CyberWei922/ESP32S3_KVM_desktop_controller/esp32/latest/docs/development_plan.md

# v0.5.0-dev.22 开发计划

## 阶段A：规格冻结

- [x] 视觉年代固定为System 7，并辅以少量System 1元素。
- [x] 屏幕语言固定为纯英文。
- [x] UI结构冻结为SYSTEM、WEATHER、MARKETS三页仪表盘。
- [x] 固定LVGL 9.3.0和ESP-IDF组件集成方式；字体与图标资源已纳入源码。
- [x] 冻结散热器四模式、按键判定、上电归一化和自动控温设计，见`cooler_control_spec.md`。
- [ ] 实测散热器双击、关机长按、组间隔和上电等待时序。
- [x] 关闭状态要求物理熄灭背光，不接受仅绘制黑色画面。
- [x] ILI9341V软件背光命令实机无效，排除纯SPI控制方案。
- [x] BLK接地电流实测约0.2mA，GPIO15开漏直接控制已完成实机开/关验证。
- [ ] 完成GPIO15重复开关与长时间运行验收。

## 阶段B：显示系统

- [x] 创建ESP-IDF v6.1工程。
- [x] 接入LVGL和ILI9341 flush回调。
- [x] 完成SYSTEM、WEATHER、MARKETS三页复古界面并验证编译。
- [ ] 刷写实机后检查内存、帧率和连续运行。

## 阶段C：服务移植

- [x] 按模块移植状态、Wi-Fi、WebSocket、protocol v1和按钮驱动。
- [x] 建立语义事件队列和单一LVGL任务。
- [x] 加入两路继电器安全驱动与截止保护。
- [x] 加入dashboard序号校验、Windows主源和Mac备用源切换。
- [x] 加入display_sleep/display_wake能力协商和结果汇总。

## 阶段D：页面与交互

- [x] 完成SYSTEM、WEATHER、MARKETS三页仪表盘。
- [x] 启用中键单击下一页、双击上一页。
- [x] 完成左键KVM状态机。
- [x] 按`cooler_control_spec.md`实现GPIO8状态机；继电器延时不放入UI任务。
- [x] 加入错误、离线、未知、校准和冷却反馈。
- [ ] 完成刷写后的整机交互验收。

## 阶段E：首版整机验收

- 联调Mac、Windows、DDC和USB；确认散热器UI不触发GPIO8。
- 完成100次KVM切换与24小时运行。
- 验收后冻结版本，更新根目录路线和版本记录。

## 当前扩展：双主机显示待机与唤醒

- [x] 实测确认：X41Q在仍有Windows DP信号时会从Mac自动跳到DP；所有输入均停止后进入闪灯待机。
- [x] 冻结“双客户端停止视频输出、只唤醒目标主机”的设计，见`display_sleep_plan.md`。
- [x] 以protocol v1可选能力协商扩展`display_sleep`和`display_wake`命令及可诊断结果。
- [x] Mac客户端实现只关闭/恢复显示输出，不让整机睡眠。
- [ ] Windows托盘客户端实现只关闭/恢复显示输出，并在黑屏期间保持在线。
- [x] ESP32实现双客户端并行休眠、结果汇总、目标单机唤醒和错误状态机。
- [x] 将左键长按背光开关与显示待机状态机绑定；黑屏期间锁定所有按键，只保留左键长按唤醒。
- [x] 唤醒时默认只恢复关屏前当前主机的视频输出，不同时恢复两路。
- [ ] 完成20次待机及Mac/Windows各10次定向唤醒验收。

## 暂缓项：刷新同步背光补偿

状态：已写入`v0.5.0-dev.22`固件和macOS客户端，等待Windows客户端实现与三端实机验收。

### 已确认事实

- 厂商风格隔离测试固件已实机确认：GPIO15以20kHz PWM输出时，BLK能够呈现三个清晰亮度档位，说明本机实物支持通过BLK进行PWM亮度控制。
- 最精简的软件SPI测试在真实像素刷新瞬间仍会闪烁，因此问题不依赖LVGL、Wi-Fi或DMA；刷新期间的电气负载变化仍是待补偿对象。

### 临时参数（不是最终校准值）

- PWM频率：20kHz。
- 静态/非刷新亮度：60%占空比，暂时固定。
- 刷新期间亮度：初始验证可从100%占空比开始，最终值必须根据实机结果调整。
- 这些参数只能集中定义，禁止散落为魔法数字。

### 计划实现方式

- 在一次有效画面更新开始、首笔像素传输之前切换到“刷新亮度”。
- 在本次画面更新的最后一个刷新区块完成后恢复60%“静态亮度”。
- 不得在同一次LVGL更新的每个分块之间反复恢复60%，避免补偿本身产生闪烁。
- 背光开关状态优先级高于补偿：用户关闭背光后，任何刷新都不得重新点亮。

### 必须完成的刷新面积实测

刷新面积可能改变瞬时负载、传输持续时间和肉眼感受到的亮度下降，因此不能假设所有区块共用同一个补偿值。实施时至少分别记录：

1. 极小刷新：单个状态图标、短文本或中央小方块。
2. 中等刷新：一行Live Data、进度条或一个信息框。
3. 多分块刷新：同一UI状态变更触发多个区域连续传输。
4. 全屏刷新：开机页切换或完整界面重绘。

每组记录刷新像素数、总传输时长、静态占空比、刷新占空比以及肉眼结果（偏暗、持平或偏亮）。如果不同面积所需补偿明显不同，再决定采用：

- 单一固定刷新占空比；或
- 按刷新像素数/传输时长分为小、中、全屏三档补偿。

### 验收条件

- 小区域、中区域、多分块和全屏刷新时均无肉眼可见的变暗或过亮。
- 连续遥测刷新期间亮度稳定，PWM本身无可见闪烁或啸叫。
- 反复刷新不会破坏左键长按背光关闭与恢复功能。
