CyberWei922/ESP32S3_KVM_desktop_controller/cad_enclosure/history_and_generation/apple_retro_hybrid/generator/previews/macintosh_compact_concept_v1.png

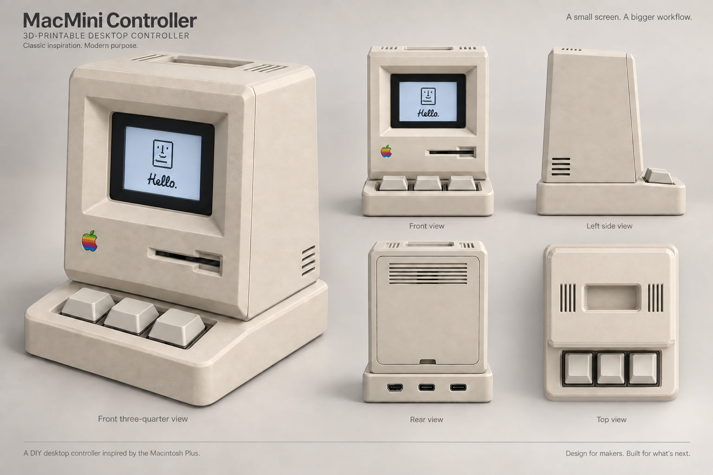
cad_enclosure/history_and_generation/apple_retro_hybrid/generator/previews/macintosh_compact_concept_v1.png
