CyberWei922/ESP32S3_KVM_desktop_controller/cad_enclosure/history_and_generation/apple_retro_hybrid/generator/previews/internal_layout_preview.png

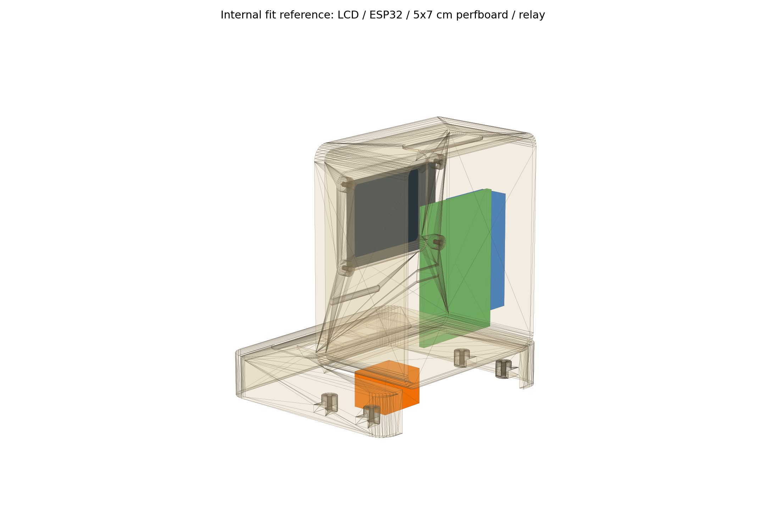
cad_enclosure/history_and_generation/apple_retro_hybrid/generator/previews/internal_layout_preview.png
