CyberWei922/ESP32S3_KVM_desktop_controller/cad_enclosure/history_and_generation/apple_retro_hybrid/generator/previews/lower_base_no_locator_v118.png

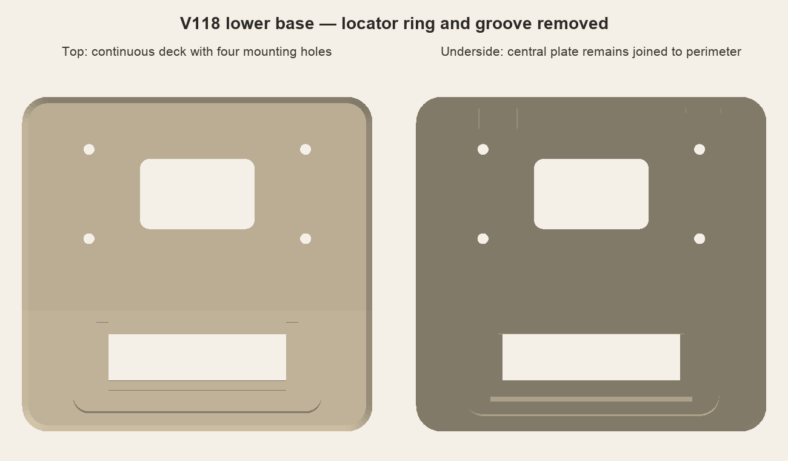
cad_enclosure/history_and_generation/apple_retro_hybrid/generator/previews/lower_base_no_locator_v118.png
