CyberWei922/ESP32S3_KVM_desktop_controller/cad_enclosure/history_and_generation/apple_retro_hybrid/generator/previews/macintosh_controller_v14_geometry.png

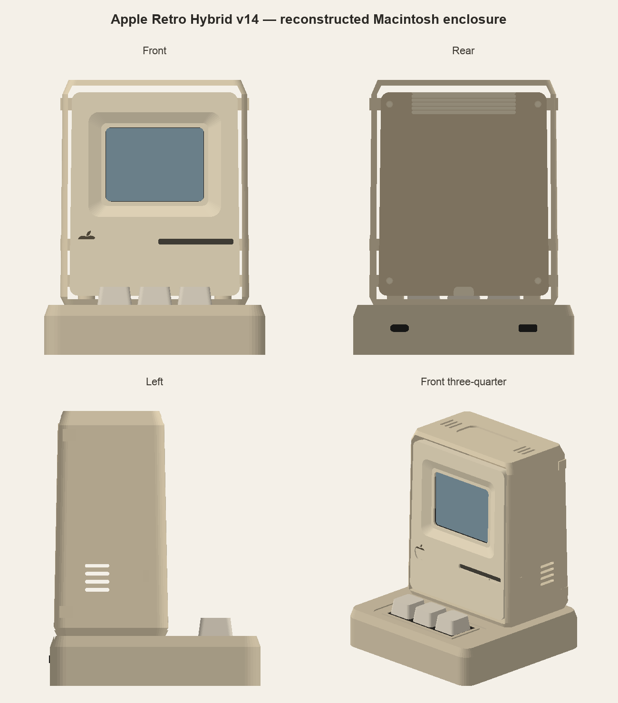
cad_enclosure/history_and_generation/apple_retro_hybrid/generator/previews/macintosh_controller_v14_geometry.png
