CyberWei922/ESP32S3_KVM_desktop_controller/cad_enclosure/history_and_generation/apple_retro_hybrid/generator/previews/rear_shell_bevel_v115.png

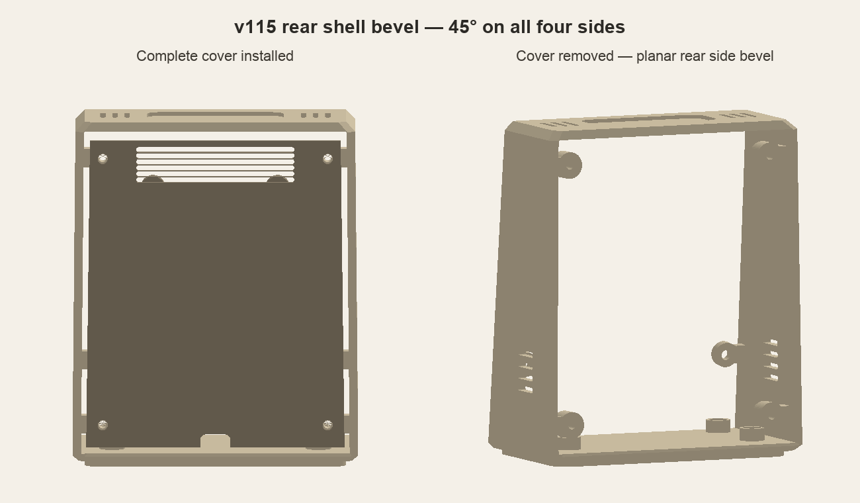
cad_enclosure/history_and_generation/apple_retro_hybrid/generator/previews/rear_shell_bevel_v115.png
