CyberWei922/ESP32S3_KVM_desktop_controller/esp32/latest/main/kvm_font_unscii_10.c

/* Generated from LVGL unscii-8 with nearest-neighbor integer pixels. */
#include "lvgl.h"

static LV_ATTRIBUTE_LARGE_CONST const uint8_t glyph_bitmap[] = {
    0x00,0x00,0x00,0x00,0x00,0x00,0x00,0x00,0x00,0x00,0x00,0x00,0x00,0x0e,0x03,0x80,
    0xe0,0x38,0x0e,0x03,0x80,0xe0,0x00,0x0e,0x00,0x00,0x31,0x8c,0x63,0x18,0xc6,0x00,
    0x00,0x00,0x00,0x00,0x00,0x00,0x00,0x37,0x0d,0xc3,0x73,0xfe,0x37,0x3f,0xef,0xf8,
    0xdc,0x37,0x00,0x00,0x0e,0x03,0x81,0xf8,0xc0,0x1f,0x00,0x60,0x18,0xfc,0x0e,0x00,
    0x00,0x00,0x00,0x0e,0x1b,0x9c,0x0e,0x06,0x01,0x80,0xc6,0xe1,0x80,0x00,0x1e,0x07,
    0x83,0x70,0x78,0x39,0xbb,0xce,0xf3,0x9c,0x39,0x80,0x00,0x0e,0x03,0x80,0xe0,0x60,
    0x00,0x00,0x00,0x00,0x00,0x00,0x00,0x00,0x07,0x01,0xc0,0xe0,0x60,0x18,0x06,0x01,
    0x80,0x38,0x07,0x00,0x00,0x18,0x06,0x00,0xe0,0x1c,0x07,0x01,0xc0,0x70,0x38,0x18,
    0x00,0x00,0x00,0x00,0x03,0x18,0x7c,0xff,0xc7,0xc1,0xf0,0xc6,0x00,0x00,0x00,0x00,
    0x00,0x00,0xe0,0x38,0x3f,0x83,0x80,0xe0,0x38,0x00,0x00,0x00,0x00,0x00,0x00,0x00,
    0x00,0x00,0x00,0x00,0x00,0x38,0x0e,0x06,0x00,0x00,0x00,0x00,0x00,0x00,0x3f,0x80,
    0x00,0x00,0x00,0x00,0x00,0x00,0x00,0x00,0x00,0x00,0x00,0x00,0x00,0x00,0x00,0x38,
    0x0e,0x00,0x00,0x00,0xc0,0x30,0x18,0x1c,0x0e,0x06,0x01,0x80,0xc0,0xe0,0x00,0x00,
    0x1f,0x07,0xc3,0x18,0xde,0x39,0x8c,0x63,0x18,0xc6,0x1f,0x00,0x00,0x0e,0x03,0x81,
    0xe0,0x38,0x0e,0x03,0x80,0xe0,0x38,0x3f,0x80,0x00,0x1f,0x07,0xc3,0x18,0x1c,0x0e,
    0x06,0x01,0x80,0xc0,0x3f,0x80,0x00,0x1f,0x07,0xc3,0x18,0x06,0x0f,0x00,0x60,0x18,
    0xc6,0x1f,0x00,0x00,0x0f,0x03,0xc1,0xf0,0xdc,0xe7,0x3f,0xef,0xf8,0x1c,0x07,0x00,
    0x00,0x3f,0x8f,0xe3,0x00,0xfc,0x01,0x80,0x60,0x18,0xc6,0x1f,0x00,0x00,0x0f,0x03,
    0xc1,0x80,0xc0,0x3f,0x0c,0x63,0x18,0xc6,0x1f,0x00,0x00,0x3f,0x8f,0xe0,0x18,0x06,
    0x07,0x03,0x80,0xe0,0x38,0x0e,0x00,0x00,0x1f,0x07,0xc3,0x18,0xc6,0x1f,0x0c,0x63,
    0x18,0xc6,0x1f,0x00,0x00,0x1f,0x07,0xc3,0x18,0xc6,0x1f,0x80,0x60,0x18,0x1c,0x1e,
    0x00,0x00,0x00,0x00,0x00,0xe0,0x38,0x00,0x00,0x00,0x00,0x38,0x0e,0x00,0x00,0x00,
    0x00,0x00,0xe0,0x38,0x00,0x00,0x00,0x00,0x38,0x0e,0x06,0x00,0x07,0x01,0xc0,0xe0,
    0x60,0x30,0x06,0x01,0x80,0x38,0x07,0x00,0x00,0x00,0x00,0x00,0x00,0xfe,0x00,0x0f,
    0xe3,0xf8,0x00,0x00,0x00,0x00,0x30,0x0c,0x01,0x80,0x38,0x07,0x03,0x80,0xe0,0x60,
    0x30,0x00,0x00,0x1f,0x07,0xc3,0x18,0x06,0x07,0x03,0x80,0xe0,0x00,0x0e,0x00,0x00,
    0x3f,0x0f,0xce,0x1b,0xbe,0xef,0xbb,0xee,0xfb,0x80,0x3f,0x00,0x00,0x0e,0x03,0x81,
    0xf0,0xc6,0x31,0x8f,0xe3,0xf8,0xc6,0x31,0x80,0x00,0x3f,0x0f,0xc3,0x18,0xc6,0x3f,
    0x0c,0x63,0x18,0xc6,0x3f,0x00,0x00,0x1f,0x07,0xc3,0x18,0xc0,0x30,0x0c,0x03,0x00,
    0xc6,0x1f,0x00,0x00,0x3e,0x0f,0x83,0x70,0xc6,0x31,0x8c,0x63,0x18,0xdc,0x3e,0x00,
    0x00,0x3f,0x8f,0xe3,0x00,0xc0,0x3f,0x0c,0x03,0x00,0xc0,0x3f,0x80,0x00,0x3f,0x8f,
    0xe3,0x00,0xc0,0x3f,0x0c,0x03,0x00,0xc0,0x30,0x00,0x00,0x1f,0x07,0xc3,0x18,0xc0,
    0x37,0x8c,0x63,0x18,0xc6,0x1f,0x80,0x00,0x31,0x8c,0x63,0x18,0xc6,0x3f,0x8c,0x63,
    0x18,0xc6,0x31,0x80,0x00,0x3f,0x8f,0xe0,0xe0,0x38,0x0e,0x03,0x80,0xe0,0x38,0x3f,
    0x80,0x00,0x01,0x80,0x60,0x18,0x06,0x01,0x80,0x60,0x18,0xc6,0x1f,0x00,0x00,0xe1,
    0xb8,0x6e,0x73,0xb8,0xf8,0x3b,0x8e,0xe3,0x9c,0xe1,0x80,0x00,0x30,0x0c,0x03,0x00,
    0xc0,0x30,0x0c,0x03,0x00,0xc0,0x3f,0x80,0x00,0xe1,0xb8,0x6f,0x7b,0xfe,0xe9,0xb8,
    0x6e,0x1b,0x86,0xe1,0x80,0x00,0xe1,0xb8,0x6f,0x1b,0xe6,0xef,0xb9,0xee,0x7b,0x86,
    0xe1,0x80,0x00,0x1f,0x07,0xc3,0x18,0xc6,0x31,0x8c,0x63,0x18,0xc6,0x1f,0x00,0x00,
    0x3f,0x0f,0xc3,0x18,0xc6,0x3f,0x0c,0x03,0x00,0xc0,0x30,0x00,0x00,0x1f,0x07,0xc3,
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
};

static const lv_font_fmt_txt_glyph_dsc_t glyph_dsc[] = {
    {.bitmap_index = 0, .adv_w = 0, .box_w = 0, .box_h = 0, .ofs_x = 0, .ofs_y = 0},
    {.bitmap_index = 0, .adv_w = 160, .box_w = 10, .box_h = 10, .ofs_x = 0, .ofs_y = 0},
    {.bitmap_index = 13, .adv_w = 160, .box_w = 10, .box_h = 10, .ofs_x = 0, .ofs_y = 0},
    {.bitmap_index = 26, .adv_w = 160, .box_w = 10, .box_h = 10, .ofs_x = 0, .ofs_y = 0},
    {.bitmap_index = 39, .adv_w = 160, .box_w = 10, .box_h = 10, .ofs_x = 0, .ofs_y = 0},
    {.bitmap_index = 52, .adv_w = 160, .box_w = 10, .box_h = 10, .ofs_x = 0, .ofs_y = 0},
    {.bitmap_index = 65, .adv_w = 160, .box_w = 10, .box_h = 10, .ofs_x = 0, .ofs_y = 0},
    {.bitmap_index = 78, .adv_w = 160, .box_w = 10, .box_h = 10, .ofs_x = 0, .ofs_y = 0},
    {.bitmap_index = 91, .adv_w = 160, .box_w = 10, .box_h = 10, .ofs_x = 0, .ofs_y = 0},
    {.bitmap_index = 104, .adv_w = 160, .box_w = 10, .box_h = 10, .ofs_x = 0, .ofs_y = 0},
    {.bitmap_index = 117, .adv_w = 160, .box_w = 10, .box_h = 10, .ofs_x = 0, .ofs_y = 0},
    {.bitmap_index = 130, .adv_w = 160, .box_w = 10, .box_h = 10, .ofs_x = 0, .ofs_y = 0},
    {.bitmap_index = 143, .adv_w = 160, .box_w = 10, .box_h = 10, .ofs_x = 0, .ofs_y = 0},
    {.bitmap_index = 156, .adv_w = 160, .box_w = 10, .box_h = 10, .ofs_x = 0, .ofs_y = 0},
    {.bitmap_index = 169, .adv_w = 160, .box_w = 10, .box_h = 10, .ofs_x = 0, .ofs_y = 0},
    {.bitmap_index = 182, .adv_w = 160, .box_w = 10, .box_h = 10, .ofs_x = 0, .ofs_y = 0},
    {.bitmap_index = 195, .adv_w = 160, .box_w = 10, .box_h = 10, .ofs_x = 0, .ofs_y = 0},
    {.bitmap_index = 208, .adv_w = 160, .box_w = 10, .box_h = 10, .ofs_x = 0, .ofs_y = 0},
    {.bitmap_index = 221, .adv_w = 160, .box_w = 10, .box_h = 10, .ofs_x = 0, .ofs_y = 0},
    {.bitmap_index = 234, .adv_w = 160, .box_w = 10, .box_h = 10, .ofs_x = 0, .ofs_y = 0},
    {.bitmap_index = 247, .adv_w = 160, .box_w = 10, .box_h = 10, .ofs_x = 0, .ofs_y = 0},
    {.bitmap_index = 260, .adv_w = 160, .box_w = 10, .box_h = 10, .ofs_x = 0, .ofs_y = 0},
    {.bitmap_index = 273, .adv_w = 160, .box_w = 10, .box_h = 10, .ofs_x = 0, .ofs_y = 0},
    {.bitmap_index = 286, .adv_w = 160, .box_w = 10, .box_h = 10, .ofs_x = 0, .ofs_y = 0},
    {.bitmap_index = 299, .adv_w = 160, .box_w = 10, .box_h = 10, .ofs_x = 0, .ofs_y = 0},
    {.bitmap_index = 312, .adv_w = 160, .box_w = 10, .box_h = 10, .ofs_x = 0, .ofs_y = 0},
    {.bitmap_index = 325, .adv_w = 160, .box_w = 10, .box_h = 10, .ofs_x = 0, .ofs_y = 0},
    {.bitmap_index = 338, .adv_w = 160, .box_w = 10, .box_h = 10, .ofs_x = 0, .ofs_y = 0},
    {.bitmap_index = 351, .adv_w = 160, .box_w = 10, .box_h = 10, .ofs_x = 0, .ofs_y = 0},
    {.bitmap_index = 364, .adv_w = 160, .box_w = 10, .box_h = 10, .ofs_x = 0, .ofs_y = 0},
    {.bitmap_index = 377, .adv_w = 160, .box_w = 10, .box_h = 10, .ofs_x = 0, .ofs_y = 0},
    {.bitmap_index = 390, .adv_w = 160, .box_w = 10, .box_h = 10, .ofs_x = 0, .ofs_y = 0},
    {.bitmap_index = 403, .adv_w = 160, .box_w = 10, .box_h = 10, .ofs_x = 0, .ofs_y = 0},
    {.bitmap_index = 416, .adv_w = 160, .box_w = 10, .box_h = 10, .ofs_x = 0, .ofs_y = 0},
    {.bitmap_index = 429, .adv_w = 160, .box_w = 10, .box_h = 10, .ofs_x = 0, .ofs_y = 0},
    {.bitmap_index = 442, .adv_w = 160, .box_w = 10, .box_h = 10, .ofs_x = 0, .ofs_y = 0},
    {.bitmap_index = 455, .adv_w = 160, .box_w = 10, .box_h = 10, .ofs_x = 0, .ofs_y = 0},
    {.bitmap_index = 468, .adv_w = 160, .box_w = 10, .box_h = 10, .ofs_x = 0, .ofs_y = 0},
    {.bitmap_index = 481, .adv_w = 160, .box_w = 10, .box_h = 10, .ofs_x = 0, .ofs_y = 0},
    {.bitmap_index = 494, .adv_w = 160, .box_w = 10, .box_h = 10, .ofs_x = 0, .ofs_y = 0},
    {.bitmap_index = 507, .adv_w = 160, .box_w = 10, .box_h = 10, .ofs_x = 0, .ofs_y = 0},
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
    {.bitmap_index = 1105, .adv_w = 160, .box_w = 10, .box_h = 10, .ofs_x = 0, .ofs_y = 0},
    {.bitmap_index = 1118, .adv_w = 160, .box_w = 10, .box_h = 10, .ofs_x = 0, .ofs_y = 0},
    {.bitmap_index = 1131, .adv_w = 160, .box_w = 10, .box_h = 10, .ofs_x = 0, .ofs_y = 0},
    {.bitmap_index = 1144, .adv_w = 160, .box_w = 10, .box_h = 10, .ofs_x = 0, .ofs_y = 0},
    {.bitmap_index = 1157, .adv_w = 160, .box_w = 10, .box_h = 10, .ofs_x = 0, .ofs_y = 0},
    {.bitmap_index = 1170, .adv_w = 160, .box_w = 10, .box_h = 10, .ofs_x = 0, .ofs_y = 0},
    {.bitmap_index = 1183, .adv_w = 160, .box_w = 10, .box_h = 10, .ofs_x = 0, .ofs_y = 0},
    {.bitmap_index = 1196, .adv_w = 160, .box_w = 10, .box_h = 10, .ofs_x = 0, .ofs_y = 0},
    {.bitmap_index = 1209, .adv_w = 160, .box_w = 10, .box_h = 10, .ofs_x = 0, .ofs_y = 0},
    {.bitmap_index = 1222, .adv_w = 160, .box_w = 10, .box_h = 10, .ofs_x = 0, .ofs_y = 0},
    {.bitmap_index = 1235, .adv_w = 160, .box_w = 10, .box_h = 10, .ofs_x = 0, .ofs_y = 0},
};

static const lv_font_fmt_txt_cmap_t cmaps[] = {
    {.range_start = 32, .range_length = 96, .glyph_id_start = 1, .unicode_list = NULL, .glyph_id_ofs_list = NULL, .list_length = 0, .type = LV_FONT_FMT_TXT_CMAP_FORMAT0_TINY}
};

static const lv_font_fmt_txt_dsc_t font_dsc = {
    .glyph_bitmap = glyph_bitmap,
    .glyph_dsc = glyph_dsc,
    .cmaps = cmaps,
    .kern_dsc = NULL,
    .kern_scale = 0,
    .cmap_num = 1,
    .bpp = 1,
    .kern_classes = 0,
    .bitmap_format = 0,
};

const lv_font_t kvm_font_unscii_10 = {
    .get_glyph_dsc = lv_font_get_glyph_dsc_fmt_txt,
    .get_glyph_bitmap = lv_font_get_bitmap_fmt_txt,
    .line_height = 10,
    .base_line = 0,
    .subpx = LV_FONT_SUBPX_NONE,
    .underline_position = 0,
    .underline_thickness = 0,
    .dsc = &font_dsc,
    .fallback = &lv_font_unscii_8,
    .user_data = NULL,
};
