CyberWei922/ESP32S3_KVM_desktop_controller/esp32/latest/main/kvm_font_unscii_12.c

/* Generated from LVGL unscii-8 with nearest-neighbor integer pixels. */
#include "lvgl.h"

static LV_ATTRIBUTE_LARGE_CONST const uint8_t glyph_bitmap[] = {
    0x00,0x00,0x00,0x00,0x00,0x00,0x00,0x00,0x00,0x00,0x00,0x00,0x00,0x00,0x00,0x00,
    0x00,0x00,0x07,0x00,0x70,0x07,0x00,0x70,0x07,0x00,0x70,0x07,0x00,0x70,0x00,0x00,
    0x70,0x07,0x00,0x00,0x38,0xe3,0x8e,0x38,0xe3,0x8e,0x38,0xe0,0x00,0x00,0x00,0x00,
    0x00,0x00,0x00,0x00,0x00,0x00,0x3b,0x83,0xb8,0x3b,0x8f,0xfe,0xff,0xe3,0xb8,0xff,
    0xef,0xfe,0x3b,0x83,0xb8,0x3b,0x80,0x00,0x07,0x00,0x70,0x1f,0xe3,0x80,0x38,0x01,
    0xf8,0x00,0xe0,0x0e,0x3f,0x80,0x70,0x07,0x00,0x00,0x00,0x00,0x00,0xe0,0xee,0x38,
    0xe3,0x80,0x70,0x1c,0x01,0xc0,0x38,0xee,0x0e,0xe0,0xe0,0x00,0x1f,0x01,0xf0,0x3b,
    0x81,0xf0,0x1f,0x03,0xce,0xe7,0x8e,0x78,0xe3,0x83,0xce,0x3c,0xe0,0x00,0x07,0x00,
    0x70,0x07,0x01,0xc0,0x1c,0x00,0x00,0x00,0x00,0x00,0x00,0x00,0x00,0x00,0x00,0x00,
    0x03,0x80,0x38,0x07,0x01,0xc0,0x1c,0x01,0xc0,0x1c,0x01,0xc0,0x07,0x00,0x38,0x03,
    0x80,0x00,0x1c,0x01,0xc0,0x07,0x00,0x38,0x03,0x80,0x38,0x03,0x80,0x38,0x07,0x01,
    0xc0,0x1c,0x00,0x00,0x00,0x00,0x00,0x38,0xe1,0xf8,0x1f,0x8f,0xff,0x1f,0x81,0xf8,
    0x38,0xe0,0x00,0x00,0x00,0x00,0x00,0x00,0x00,0x07,0x00,0x70,0x07,0x03,0xfe,0x07,
    0x00,0x70,0x07,0x00,0x00,0x00,0x00,0x00,0x00,0x00,0x00,0x00,0x00,0x00,0x00,0x00,
    0x00,0x00,0x00,0x00,0x07,0x00,0x70,0x07,0x01,0xc0,0x00,0x00,0x00,0x00,0x00,0x00,
    0x00,0x03,0xfe,0x00,0x00,0x00,0x00,0x00,0x00,0x00,0x00,0x00,0x00,0x00,0x00,0x00,
    0x00,0x00,0x00,0x00,0x00,0x00,0x00,0x00,0x07,0x00,0x70,0x07,0x00,0x00,0x00,0x70,
    0x07,0x00,0xe0,0x38,0x03,0x80,0x70,0x1c,0x01,0xc0,0x38,0x0e,0x00,0xe0,0x00,0x00,
    0x1f,0x81,0xf8,0x38,0xe3,0xbe,0x3b,0xe3,0xce,0x38,0xe3,0x8e,0x38,0xe1,0xf8,0x1f,
    0x80,0x00,0x07,0x00,0x70,0x1f,0x00,0x70,0x07,0x00,0x70,0x07,0x00,0x70,0x07,0x03,
    0xfe,0x3f,0xe0,0x00,0x1f,0x81,0xf8,0x38,0xe0,0x38,0x03,0x80,0x70,0x1c,0x01,0xc0,
    0x38,0x03,0xfe,0x3f,0xe0,0x00,0x1f,0x81,0xf8,0x38,0xe0,0x0e,0x00,0xe0,0x78,0x00,
    0xe0,0x0e,0x38,0xe1,0xf8,0x1f,0x80,0x00,0x07,0x80,0x78,0x1f,0x83,0xb8,0x3b,0x8e,
    0x38,0xff,0xef,0xfe,0x03,0x80,0x38,0x03,0x80,0x00,0x3f,0xe3,0xfe,0x38,0x03,0xf8,
    0x3f,0x80,0x0e,0x00,0xe0,0x0e,0x38,0xe1,0xf8,0x1f,0x80,0x00,0x07,0x80,0x78,0x1c,
    0x03,0x80,0x38,0x03,0xf8,0x38,0xe3,0x8e,0x38,0xe1,0xf8,0x1f,0x80,0x00,0x3f,0xe3,
    0xfe,0x00,0xe0,0x0e,0x00,0xe0,0x38,0x07,0x00,0x70,0x07,0x00,0x70,0x07,0x00,0x00,
    0x1f,0x81,0xf8,0x38,0xe3,0x8e,0x38,0xe1,0xf8,0x38,0xe3,0x8e,0x38,0xe1,0xf8,0x1f,
    0x80,0x00,0x1f,0x81,0xf8,0x38,0xe3,0x8e,0x38,0xe1,0xfe,0x00,0xe0,0x0e,0x03,0x81,
    0xf0,0x1f,0x00,0x00,0x00,0x00,0x00,0x07,0x00,0x70,0x07,0x00,0x00,0x00,0x00,0x00,
    0x07,0x00,0x70,0x07,0x00,0x00,0x00,0x00,0x00,0x07,0x00,0x70,0x07,0x00,0x00,0x00,
    0x00,0x00,0x07,0x00,0x70,0x07,0x01,0xc0,0x03,0x80,0x38,0x07,0x01,0xc0,0x1c,0x03,
    0x80,0x1c,0x01,0xc0,0x07,0x00,0x38,0x03,0x80,0x00,0x00,0x00,0x00,0x00,0x03,0xfe,
    0x3f,0xe0,0x00,0x3f,0xe3,0xfe,0x00,0x00,0x00,0x00,0x00,0x00,0x38,0x03,0x80,0x1c,
    0x00,0x70,0x07,0x00,0x38,0x07,0x00,0x70,0x1c,0x03,0x80,0x38,0x00,0x00,0x1f,0x81,
    0xf8,0x38,0xe0,0x0e,0x00,0xe0,0x38,0x07,0x00,0x70,0x00,0x00,0x70,0x07,0x00,0x00,
    0x3f,0x83,0xf8,0xe0,0xee,0x7e,0xe7,0xee,0x7e,0xe7,0xee,0x7e,0xe0,0x03,0xf8,0x3f,
    0x80,0x00,0x07,0x00,0x70,0x1f,0x83,0x8e,0x38,0xe3,0x8e,0x3f,0xe3,0xfe,0x38,0xe3,
    0x8e,0x38,0xe0,0x00,0x3f,0x83,0xf8,0x38,0xe3,0x8e,0x38,0xe3,0xf8,0x38,0xe3,0x8e,
    0x38,0xe3,0xf8,0x3f,0x80,0x00,0x1f,0x81,0xf8,0x38,0xe3,0x80,0x38,0x03,0x80,0x38,
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
};

static const lv_font_fmt_txt_glyph_dsc_t glyph_dsc[] = {
    {.bitmap_index = 0, .adv_w = 0, .box_w = 0, .box_h = 0, .ofs_x = 0, .ofs_y = 0},
    {.bitmap_index = 0, .adv_w = 192, .box_w = 12, .box_h = 12, .ofs_x = 0, .ofs_y = 0},
    {.bitmap_index = 18, .adv_w = 192, .box_w = 12, .box_h = 12, .ofs_x = 0, .ofs_y = 0},
    {.bitmap_index = 36, .adv_w = 192, .box_w = 12, .box_h = 12, .ofs_x = 0, .ofs_y = 0},
    {.bitmap_index = 54, .adv_w = 192, .box_w = 12, .box_h = 12, .ofs_x = 0, .ofs_y = 0},
    {.bitmap_index = 72, .adv_w = 192, .box_w = 12, .box_h = 12, .ofs_x = 0, .ofs_y = 0},
    {.bitmap_index = 90, .adv_w = 192, .box_w = 12, .box_h = 12, .ofs_x = 0, .ofs_y = 0},
    {.bitmap_index = 108, .adv_w = 192, .box_w = 12, .box_h = 12, .ofs_x = 0, .ofs_y = 0},
    {.bitmap_index = 126, .adv_w = 192, .box_w = 12, .box_h = 12, .ofs_x = 0, .ofs_y = 0},
    {.bitmap_index = 144, .adv_w = 192, .box_w = 12, .box_h = 12, .ofs_x = 0, .ofs_y = 0},
    {.bitmap_index = 162, .adv_w = 192, .box_w = 12, .box_h = 12, .ofs_x = 0, .ofs_y = 0},
    {.bitmap_index = 180, .adv_w = 192, .box_w = 12, .box_h = 12, .ofs_x = 0, .ofs_y = 0},
    {.bitmap_index = 198, .adv_w = 192, .box_w = 12, .box_h = 12, .ofs_x = 0, .ofs_y = 0},
    {.bitmap_index = 216, .adv_w = 192, .box_w = 12, .box_h = 12, .ofs_x = 0, .ofs_y = 0},
    {.bitmap_index = 234, .adv_w = 192, .box_w = 12, .box_h = 12, .ofs_x = 0, .ofs_y = 0},
    {.bitmap_index = 252, .adv_w = 192, .box_w = 12, .box_h = 12, .ofs_x = 0, .ofs_y = 0},
    {.bitmap_index = 270, .adv_w = 192, .box_w = 12, .box_h = 12, .ofs_x = 0, .ofs_y = 0},
    {.bitmap_index = 288, .adv_w = 192, .box_w = 12, .box_h = 12, .ofs_x = 0, .ofs_y = 0},
    {.bitmap_index = 306, .adv_w = 192, .box_w = 12, .box_h = 12, .ofs_x = 0, .ofs_y = 0},
    {.bitmap_index = 324, .adv_w = 192, .box_w = 12, .box_h = 12, .ofs_x = 0, .ofs_y = 0},
    {.bitmap_index = 342, .adv_w = 192, .box_w = 12, .box_h = 12, .ofs_x = 0, .ofs_y = 0},
    {.bitmap_index = 360, .adv_w = 192, .box_w = 12, .box_h = 12, .ofs_x = 0, .ofs_y = 0},
    {.bitmap_index = 378, .adv_w = 192, .box_w = 12, .box_h = 12, .ofs_x = 0, .ofs_y = 0},
    {.bitmap_index = 396, .adv_w = 192, .box_w = 12, .box_h = 12, .ofs_x = 0, .ofs_y = 0},
    {.bitmap_index = 414, .adv_w = 192, .box_w = 12, .box_h = 12, .ofs_x = 0, .ofs_y = 0},
    {.bitmap_index = 432, .adv_w = 192, .box_w = 12, .box_h = 12, .ofs_x = 0, .ofs_y = 0},
    {.bitmap_index = 450, .adv_w = 192, .box_w = 12, .box_h = 12, .ofs_x = 0, .ofs_y = 0},
    {.bitmap_index = 468, .adv_w = 192, .box_w = 12, .box_h = 12, .ofs_x = 0, .ofs_y = 0},
    {.bitmap_index = 486, .adv_w = 192, .box_w = 12, .box_h = 12, .ofs_x = 0, .ofs_y = 0},
    {.bitmap_index = 504, .adv_w = 192, .box_w = 12, .box_h = 12, .ofs_x = 0, .ofs_y = 0},
    {.bitmap_index = 522, .adv_w = 192, .box_w = 12, .box_h = 12, .ofs_x = 0, .ofs_y = 0},
    {.bitmap_index = 540, .adv_w = 192, .box_w = 12, .box_h = 12, .ofs_x = 0, .ofs_y = 0},
    {.bitmap_index = 558, .adv_w = 192, .box_w = 12, .box_h = 12, .ofs_x = 0, .ofs_y = 0},
    {.bitmap_index = 576, .adv_w = 192, .box_w = 12, .box_h = 12, .ofs_x = 0, .ofs_y = 0},
    {.bitmap_index = 594, .adv_w = 192, .box_w = 12, .box_h = 12, .ofs_x = 0, .ofs_y = 0},
    {.bitmap_index = 612, .adv_w = 192, .box_w = 12, .box_h = 12, .ofs_x = 0, .ofs_y = 0},
    {.bitmap_index = 630, .adv_w = 192, .box_w = 12, .box_h = 12, .ofs_x = 0, .ofs_y = 0},
    {.bitmap_index = 648, .adv_w = 192, .box_w = 12, .box_h = 12, .ofs_x = 0, .ofs_y = 0},
    {.bitmap_index = 666, .adv_w = 192, .box_w = 12, .box_h = 12, .ofs_x = 0, .ofs_y = 0},
    {.bitmap_index = 684, .adv_w = 192, .box_w = 12, .box_h = 12, .ofs_x = 0, .ofs_y = 0},
    {.bitmap_index = 702, .adv_w = 192, .box_w = 12, .box_h = 12, .ofs_x = 0, .ofs_y = 0},
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
    {.bitmap_index = 1530, .adv_w = 192, .box_w = 12, .box_h = 12, .ofs_x = 0, .ofs_y = 0},
    {.bitmap_index = 1548, .adv_w = 192, .box_w = 12, .box_h = 12, .ofs_x = 0, .ofs_y = 0},
    {.bitmap_index = 1566, .adv_w = 192, .box_w = 12, .box_h = 12, .ofs_x = 0, .ofs_y = 0},
    {.bitmap_index = 1584, .adv_w = 192, .box_w = 12, .box_h = 12, .ofs_x = 0, .ofs_y = 0},
    {.bitmap_index = 1602, .adv_w = 192, .box_w = 12, .box_h = 12, .ofs_x = 0, .ofs_y = 0},
    {.bitmap_index = 1620, .adv_w = 192, .box_w = 12, .box_h = 12, .ofs_x = 0, .ofs_y = 0},
    {.bitmap_index = 1638, .adv_w = 192, .box_w = 12, .box_h = 12, .ofs_x = 0, .ofs_y = 0},
    {.bitmap_index = 1656, .adv_w = 192, .box_w = 12, .box_h = 12, .ofs_x = 0, .ofs_y = 0},
    {.bitmap_index = 1674, .adv_w = 192, .box_w = 12, .box_h = 12, .ofs_x = 0, .ofs_y = 0},
    {.bitmap_index = 1692, .adv_w = 192, .box_w = 12, .box_h = 12, .ofs_x = 0, .ofs_y = 0},
    {.bitmap_index = 1710, .adv_w = 192, .box_w = 12, .box_h = 12, .ofs_x = 0, .ofs_y = 0},
};

static const lv_font_fmt_txt_cmap_t cmaps[] = {
    {.range_start = 32, .range_length = 96, .glyph_id_start = 1, .unicode_list = NULL, .glyph_id_ofs_list = NULL, .list_length = 0, .type = LV_FONT_FMT_TXT_CMAP_FORMAT0_TINY}
};

static const lv_font_fmt_txt_dsc_t font_dsc = {
    .glyph_bitmap = glyph_bitmap,
    .glyph_dsc = glyph_dsc,
    .cmaps = cmaps,
    .kern_dsc = NULL,
    .kern_scale = 0,
    .cmap_num = 1,
    .bpp = 1,
    .kern_classes = 0,
    .bitmap_format = 0,
};

const lv_font_t kvm_font_unscii_12 = {
    .get_glyph_dsc = lv_font_get_glyph_dsc_fmt_txt,
    .get_glyph_bitmap = lv_font_get_bitmap_fmt_txt,
    .line_height = 12,
    .base_line = 0,
    .subpx = LV_FONT_SUBPX_NONE,
    .underline_position = 0,
    .underline_thickness = 0,
    .dsc = &font_dsc,
    .fallback = &lv_font_unscii_8,
    .user_data = NULL,
};
